LeadSeason/C4/assets/images/IMG03.jpg

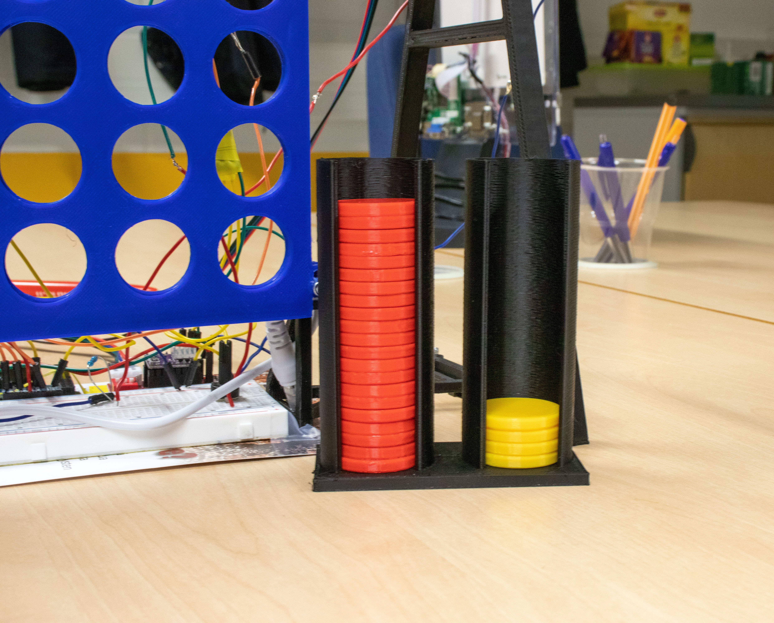
assets/images/IMG03.jpg
